gkeeth/sequencer/src/sequencer/switch.h

#ifndef SWITCH_H
#define SWITCH_H

#include <stdint.h>
#include <stdbool.h>

#define NUM_DEBOUNCE_CYCLES 20

// SKIP is 3.3V, RESET is 0V
typedef enum {
    SWITCH_RESET = 0,
    SWITCH_SKIP = 1
} skip_reset_switch;

// PLAY is 3.3V, RESET is 0V
typedef enum {
    SWITCH_STEP_SKIP_RESET = 0,
    SWITCH_STEP_PLAY
} step_switch;

void switch_setup(void);

/*
* store raw values for all step switches and the skip/reset switch
* LSB is step 1
* For step switches, a 1 bit means PLAY, a 0 bit means SKIP
* For skip/reset switch, a 1 means SKIP, a 0 means RESET
*
* This function needs to be called periodically (i.e. based on a timer).
* Values are debounced after NUM_DEBOUNCE_CYCLES timer events.
*/
void store_raw_switch_state(uint32_t raw_step_values, uint32_t raw_skip_reset_value);

/*
 * returns debounced state of the step switch for the specified step (0-indexed)
 */
step_switch get_step_switch(uint32_t step);

/*
 * returns true if step is set to skip, otherwise false
 *
 * - step: step to check, 0 to NUM_STEPS
 * - step_switch_values: bitfield of step switch values, LSB is step 0. A 1 bit
 *                       means PLAY, a 0 bit means SKIP
 */
bool is_step_skipped(uint32_t step, uint32_t step_switch_values);

/*
 * returns debounced state of all step switches (LSB is first step).
 * for each step, 1 is PLAY and 0 is SKIP.
 */
uint32_t get_step_switches(void);

/*
* returns debounced state of skip/reset switch
*/
skip_reset_switch get_skip_reset_switch(void);

#endif // SWITCH_H
